SteveBz/MoonRabbit/images/MR10.jpeg

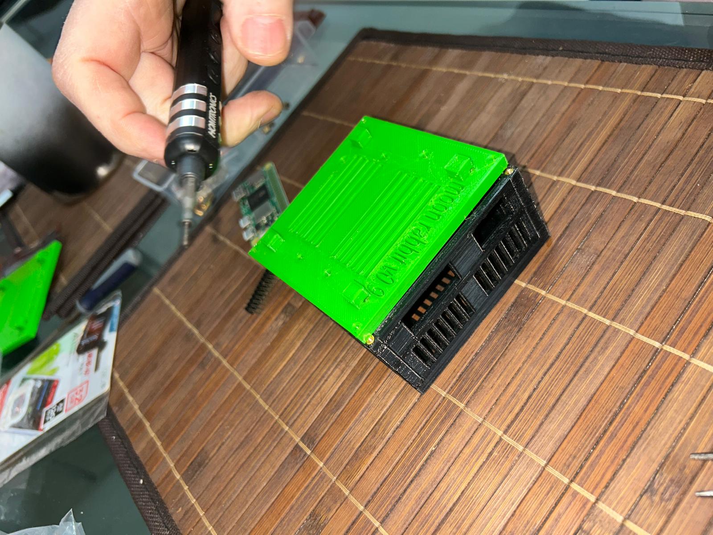
images/MR10.jpeg
