SteveBz/MoonRabbit/images/MR16.jpeg

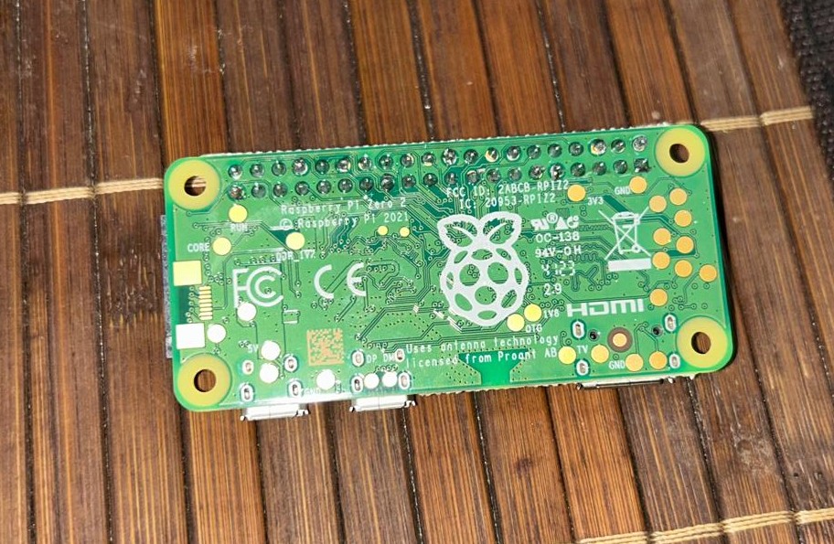
images/MR16.jpeg
