SteveBz/MoonRabbit/images/MR18.jpeg

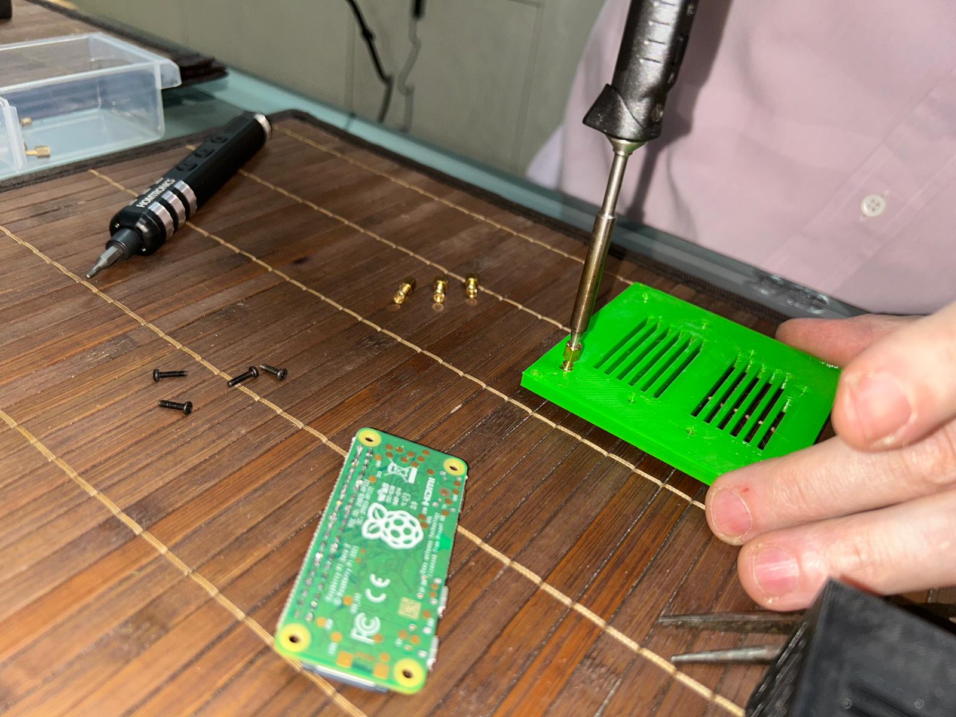
images/MR18.jpeg
