SteveBz/MoonRabbit/images/Screenshot 2024-06-08 091122.png

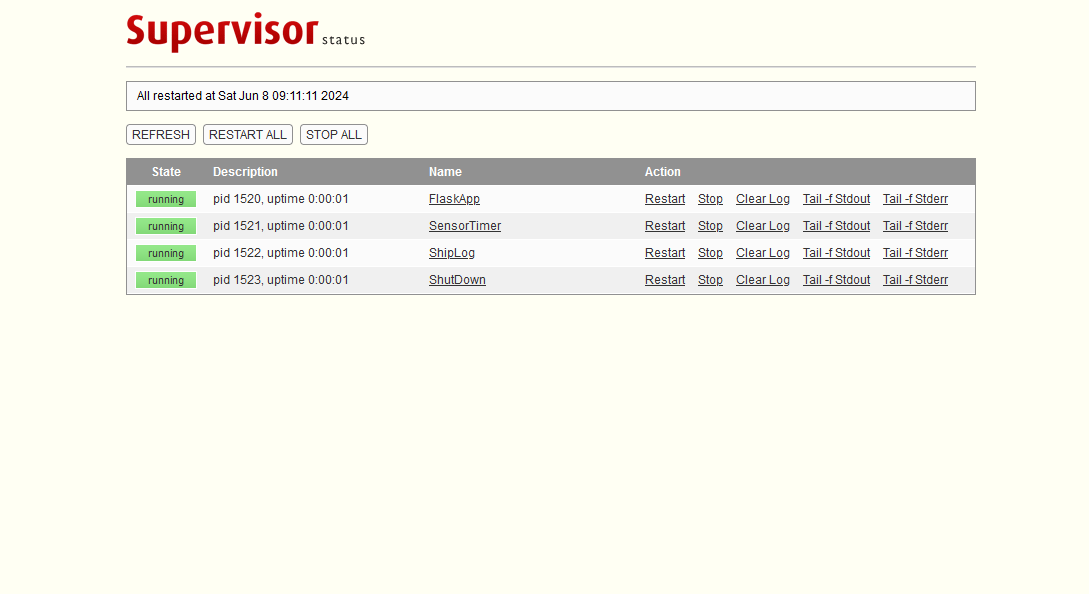
images/Screenshot 2024-06-08 091122.png
