SteveBz/MoonRabbit/class_config_mgt.py

import json
from datetime import datetime, timedelta
import fcntl
class ConfigManager:
    def __init__(self, file='config.json'):
        self.config_file = file
        self.config = self.load_config()
        #print (self.config)

        # Set runtime defaults from config
        if 'status' in self.config:
            # Define a constant for the default status
            self.DEFAULT_STATUS = self.config['status']
        
        if 'registered' in self.config:
            # Define a constant for the default registered
            self.DEFAULT_REGISTERED = self.config['registered']
        
        if 'device_id' in self.config:
            # Define a constant for the default device
            self.DEFAULT_DEVICE = self.config['device_id']
        
        if 'lat' in self.config:
            # Define a constant for the default latitude
            self.DEFAULT_LAT = float(self.config['lat'])
        
        if 'long' in self.config:
            # Define a constant for the default longitude
            self.DEFAULT_LONG = float(self.config['long'])
        
        if 'bus_address' in self.config:
            # Define a constant for the default bus address for sensor
            self.DEFAULT_BUS_ADDRESS = self.config['bus_address']

    def load_config(self):
        try:
            with open(self.config_file, 'r+') as f:
                fcntl.flock(f, fcntl.LOCK_EX)  # Acquire an exclusive lock
                try:
                    config = json.load(f)
                    fcntl.flock(f, fcntl.LOCK_UN)  # Release the lock
                except json.JSONDecodeError:
                    fcntl.flock(f, fcntl.LOCK_UN)  # Release the lock
                    config = self.create_default_config()
                    self.save_config(config)
                return config
        except FileNotFoundError:
            return self.create_default_config()
            
            
    def save_config(self, config):
        with open(self.config_file, 'w') as f:
            fcntl.flock(f, fcntl.LOCK_EX)  # Acquire an exclusive lock
            json.dump(config, f, indent=4)
            fcntl.flock(f, fcntl.LOCK_UN)  # Release the lock
            
    def create_default_config(self):
        default_config = {
            "device_id": self.DEFAULT_DEVICE,
            "registered": self.DEFAULT_REGISTERED,
            "status": self.DEFAULT_STATUS,
            "lat": self.DEFAULT_LAT,
            "long": self.DEFAULT_LONG,
            "sensor_co2": "scd30",
            "sensor_pressure": "bme280",
            "last_calibration_date": 0,
            "last_calibration_value": 0
        }
        self.save_config(default_config)
        return default_config

    def get_bus_address(self):
        # Retrieve the bus address from config
        bus_address = self.config.get("bus_address", self.DEFAULT_BUS_ADDRESS)
        
        # If bus_address is 0, save the config and return 0
        if bus_address == 0:
            print(self.config)
            self.save_config(self.config)
        
        return bus_address
        
    def set_bus_address(self, bus_address):
        self.config["bus_address"] = hex(bus_address)
        self.save_config(self.config)
        
    def get_device_id(self):
        # Retrieve the device_id from config
        device_id = self.config.get("device_id", None)
        
        # If device_id is 0, save the config and return 0
        if device_id == 0:
            self.save_config(self.config)
        
        return device_id
        
    def set_device_id(self, device_id):
        self.config["device_id"] = device_id
        self.save_config(self.config)
        
    def get_status(self):
        # Retrieve the status from config with a default value
        status = self.config.get("status", self.DEFAULT_STATUS)
        
        # If the status is the default value, save the config
        if status == self.DEFAULT_STATUS:
            self.save_config(self.config)
        
        return status

    def get_weather_source(self):
        return self.config.get("weather_source", "none")

    def set_weather_source(self, source):
        if source not in ("vantage", "ecowitt", "none"):
            raise ValueError(f"Invalid weather_source: {source}")
        self.config["weather_source"] = source
        self.save_config(self.config)

    def set_status(self, status):
        self.config["status"] = status
        self.save_config(self.config)
    
    def is_registered(self):
        # Retrieve the registered status from config with a default value
        registered = self.config.get("registered", self.DEFAULT_REGISTERED)
        
        # If registered is False, save the config
        if not registered:
            self.save_config(self.config)
        
        return registered

    def set_registered(self, registered=True):
        self.config["registered"] = registered
        self.save_config(self.config)
    def get_lat(self):
        return float(self.config.get("lat", self.DEFAULT_LAT))

    def set_lat(self, lat):
        self.config["lat"] = round(lat,4)
        self.save_config(self.config)

    def get_long(self):
        return float(self.config.get("long", self.DEFAULT_LONG))

    def set_long(self, long):
        self.config["long"] = round(long,4)
        self.save_config(self.config)

    @staticmethod
    def _aligned_start(interval):
        now = datetime.now()
        if interval == "month":
            return now.replace(day=1, hour=0, minute=0, second=0, microsecond=0)
        if interval == "day":
            return now.replace(hour=0, minute=0, second=0, microsecond=0)
        if interval == "hour":
            return now.replace(minute=0, second=0, microsecond=0)
        # "min"
        return now.replace(second=0, microsecond=0)

    def get_time_interval_values(self, interval="min"):
        if "time_intervals" not in self.config:
            self.config["time_intervals"] = {
                "month": {
                    "start":datetime.now().isoformat(),
                    "co2": 0,
                    "temperature": 0,
                    "humidity": 0,
                    "pressure": 0,
                    "count": 0
                },
                "min": {
                    "start":datetime.now().isoformat(),
                    "co2": [],
                    "temperature": [],
                    "humidity": [],
                    "pressure": [],
                },
                "hour": {
                    "start":datetime.now().isoformat(),
                    "co2": 0,
                    "temperature": 0,
                    "humidity": 0,
                    "pressure": 0,
                    "count": 0
                },
                "day": {
                    "start":datetime.now().isoformat(),
                    "co2": 0,
                    "temperature": 0,
                    "humidity": 0,
                    "pressure": 0,
                    "count": 0
                }
            }
            self.save_config(self.config)
        
        if interval in self.config["time_intervals"]:
            return self.config["time_intervals"][interval]
        else:
            raise KeyError(f"Invalid interval '{interval}' for time intervals")

    def remove_interval(self, interval):
        old_data = self.config["time_intervals"][interval]
        # Collect all keys except 'start' and 'count'
        sensor_keys = [k for k in old_data.keys() if k not in ("start", "count")]

        del self.config["time_intervals"][interval]

        new_data = {"start": self._aligned_start(interval).isoformat()}
        if interval == "min":
            for key in sensor_keys:
                new_data[key] = []
        else:
            for key in sensor_keys:
                new_data[key] = 0
            new_data["count"] = 0

        self.config["time_intervals"][interval] = new_data
        self.save_config(self.config)
        return self.config
            
    def set_time_interval_values(self, date_time, sensor_value_dict):
        if "min" not in self.config["time_intervals"]:
            self.config["time_intervals"]["min"] = {
                    "start":date_time,
                    "co2": [],
                    "temperature": [],
                    "humidity": [],
                    "pressure": [],
                }
        if "hour" not in self.config["time_intervals"]:
            self.config["time_intervals"]["hour"]= {
                "start":date_time,
                "co2": 0,
                "temperature": 0,
                "humidity": 0,
                "pressure": 0,
                "count":0
            }
        if "day" not in self.config["time_intervals"]:
            self.config["time_intervals"]["day"]= {
                "start":date_time,
                "co2": 0,
                "temperature": 0,
                "humidity": 0,
                "pressure": 0,
                "count":0
            }
        if "month" not in self.config["time_intervals"]:
            self.config["time_intervals"]["month"]= {
                "start":date_time,
                "co2": 0,
                "temperature": 0,
                "humidity": 0,
                "pressure": 0,
                "count":0
            }
            
        for interval, interval_data in self.config["time_intervals"].items():
            # 1. Update each sensor key (add if missing)
            for sensor_key, value in sensor_value_dict.items():
                if sensor_key not in interval_data:
                    if interval == "min":
                        interval_data[sensor_key] = []
                    else:
                        interval_data[sensor_key] = 0
                if interval == "min":
                    interval_data[sensor_key].append(value)
                else:
                    interval_data[sensor_key] += value

            # 2. Increment count once per interval (for non‑min)
            if interval != "min":
                if "count" not in interval_data:
                    interval_data["count"] = 0
                interval_data["count"] += 1
        self.save_config(self.config)
        return self.config


# Usage example:
if __name__ == "__main__":
    config_manager = ConfigManager()
    
    print("\nTest 10 return device ID:")
    print("Device ID:", config_manager.get_device_id())
    
    print("\nTest 20 return Latitude:")
    print("Latitude:", config_manager.get_lat())
    
    print("\nTest 30 return Longitude:")
    print("Longitude:", config_manager.get_long())

    config_manager = ConfigManager("sensor_values.json")
    print("\nTest 40 return minute subtotals:")
    # Set and get sensor values for different time intervals
    config_manager.set_time_interval_values(datetime.now(), {
        "co2": 420,
        "temperature": 22.4,
        "humidity": 47.1,
        "pressure": 1024
    } )
    print("Minutes:", config_manager.get_time_interval_values("min"))

    print("\nTest 50 return invalid time period - ERROR:")
    # Try to get an invalid time interval value
    try:
        print("Invalid key:", config_manager.get_time_interval_values("weeks"))
    except KeyError as e:
        print("Error:", e)
