SteveBz/MoonRabbit/i2c_detect.py

#!/usr/bin/python3

import os
import subprocess
import re

p = subprocess.Popen(['i2cdetect', '-y','1'],stdout=subprocess.PIPE,)
#cmdout = str(p.communicate())

for i in range(0,9):
  line = str(p.stdout.readline())

  for match in re.finditer("[0-9][0-9]:.*[0-9][0-9]", line):
    print (match.group())
